Riesi/bierdeckel/code/beercoaster/build.rs

use vergen_gitcl::{
    BuildBuilder, CargoBuilder, Emitter, GitclBuilder, RustcBuilder, SysinfoBuilder,
};

fn main() -> Result<(), Box<dyn std::error::Error>> {
    embuild::espidf::sysenv::output();
    // NOTE: This will output only the instructions specified.
    // NOTE: See the specific builder documentation for configuration options. 
    let build = BuildBuilder::all_build()?;
    let cargo = CargoBuilder::all_cargo()?;
    let gitcl = GitclBuilder::default().describe(true, true, None).dirty(true).build()?;
    let rustc = RustcBuilder::all_rustc()?;
    let si = SysinfoBuilder::all_sysinfo()?;

    Emitter::default()
        .add_instructions(&build)?
        .add_instructions(&cargo)?
        .add_instructions(&gitcl)?
        .add_instructions(&rustc)?
        .add_instructions(&si)?
        .emit()?;
    Ok(())
}
