Riesi/bierdeckel/code/flasher_gui/src/main.rs

use iced::widget::{button, center, column, combo_box, pick_list, scrollable, text_editor, space, text, progress_bar};
use iced::{Center, Element, Fill, Task, Theme};
use rfd::{AsyncFileDialog, FileHandle};

use btleplug::platform::Manager;
use btleplug::platform::Adapter;
pub mod bt_util;
use crate::bt_util::{OTAControlResponse, OTAControl};
use std::time::{Duration, SystemTime, UNIX_EPOCH};
use tokio::time;

/*
#[tokio::main]
async fn main() -> Result<(), Box<dyn Error>> {
    let manager = Manager::new().await?;
    let adapter_list = manager.adapters().await?;
    if adapter_list.is_empty() {
        eprintln!("No Bluetooth adapters found");
    }
    // Flash
    scan(&adapter_list, false).await.unwrap();

    // Delay to prevent 
    time::sleep(Duration::from_millis(4000)).await;

    // Verify
    scan(&adapter_list, true).await.unwrap();

    Ok(())
}*/

pub fn main() -> iced::Result {
    if let Some(timestamp) = option_env!("VERGEN_BUILD_TIMESTAMP") {
        println!("Build Timestamp: {timestamp}");
    }
    if let Some(describe) = option_env!("VERGEN_GIT_DESCRIBE") {
        println!("git describe: {describe}");
    }
    
    iced::run(Example::update, Example::view)
}

struct Example {
    languages: [Language;2],
    selected_language: Option<Language>,
    text: String,
    flash_file_path: Option<FileHandle>,
    bt_adapter_list: Option<Vec<Adapter>>,
    progress: f32,
    content: text_editor::Content,
}

#[derive(Debug, Clone)]
enum Message {
    Selected(Language),
    OptionHovered(Language),
    Button(Origin),
    File(Option<FileHandle>),
    Bluetooth(BTOrigin),
    Closed,
}
#[derive(Debug, Clone)]
enum Origin {
    FlashBin,
    Flash,
    Search,
}

#[derive(Debug, Clone)]
enum BTOrigin {
    SearchResult(Option<Vec<Adapter>>),
}

async fn flashy(bin_file: FileHandle) -> Option<Vec<Adapter>> {
    if let Ok(manager) = Manager::new().await {
    
        if let Ok(adapter_list) = btleplug::api::Manager::adapters(&manager).await {
            if !adapter_list.is_empty() {
                if let Err(_) = bt_util::scan(&adapter_list, false, &bin_file).await {
                    return None;
                }
                time::sleep(Duration::from_millis(4000)).await;

                // Verify
                if let Err(_) = bt_util::scan(&adapter_list, true, &bin_file).await {
                    return None;
                }
                return Some(adapter_list)
                
            }
            eprintln!("No Bluetooth adapters found");
        }
    }
    None
}

impl Example {
    fn new() -> Self {
        Self {
            languages: Language::ALL,
            selected_language: None,
            text: String::new(),
            flash_file_path: None,
            bt_adapter_list: None,
            progress: 25f32,
            content: text_editor::Content::new(),
        }
    }

    fn update(&mut self, message: Message) -> Task<Message>  {
        match message {
            Message::Button(ori) => {
                match ori {
                    Origin::Flash => {
                        Task::none()
                    }
                    Origin::FlashBin => {
                        let file_picker = AsyncFileDialog::new()
                                    .add_filter("bin", &["bin"])
                                    .set_directory(".")
                                    .pick_file();
                        Task::perform( file_picker, Message::File)
                    }
                    Origin::Search => {
                        if let None = self.bt_adapter_list {
                            if let Some(file) = &self.flash_file_path {
                                return Task::perform( flashy(file.clone()), |av| Message::Bluetooth(BTOrigin::SearchResult(av)))
                            }
                        }
                        Task::none()
                    }
                }
            }
            Message::Bluetooth(bt) => {
                match bt {    
                    BTOrigin::SearchResult(av) => {
                        if let Some(av) = av {
                            
                        }
                        Task::none()
                    }
                }
            }
            Message::File(file) => {
                if let Some(file) = file {
                    let file_path= &file.path().display();
                    println!("{}",file_path);
                    self.text = file_path.to_string();
                    self.flash_file_path = Some(file);
                }
                Task::none()
            }
            Message::Selected(language) => {
                self.selected_language = Some(language);
                self.text = language.hello().to_string();
                Task::none()
            }
            Message::OptionHovered(language) => {
                self.text = language.hello().to_string();
                Task::none()
            }
            Message::Closed => {
                self.text = self
                    .selected_language
                    .map(|language| language.hello().to_string())
                    .unwrap_or_default();
                Task::none()
            }
        }
    }

    fn view(&self) -> Element<'_, Message> {
        // Buttons
        let button_bin_picker = button("pick binary file...").on_press(Message::Button(Origin::FlashBin));
        let button_search = button("search for coasters...").on_press(Message::Button(Origin::Search));
        let button_connect = button("connect to coaster...").on_press(Message::Button(Origin::Flash));
        let button_flash = button("flash").on_press(Message::Button(Origin::Flash));

        let prog_bar = progress_bar::<Theme>(0.0..=100.0, self.progress);
        let console_log = text_editor(&self.content)
        .placeholder("Type something here...\n multi \n ine\n\nhlello").min_height(300).height(800).width(1000); //.on_action(Message::Edit);

        let scro = scrollable(column![
            console_log,
        ]).height(300);
        // let combo_box = combo_box(
        //     &self.languages,
        //     "Type a language...",
        //     self.selected_language.as_ref(),
        //     Message::Selected,
        // )
        // .on_option_hovered(Message::OptionHovered)
        // .on_close(Message::Closed)
        // .width(250);

        let combo_box = pick_list(
            self.languages,
            self.selected_language,
            Message::Selected,
        ).on_close(Message::Closed)
        .width(250);

        // Layout
        let content = column![
            button_bin_picker,
            button_search,
            button_connect,
            button_flash,
            text(&self.text),
            "What is your language?",
            combo_box,
            prog_bar,
            "Console:",
            scro,
            space().height(150),
        ]
        .width(Fill)
        .align_x(Center)
        .spacing(10);

        center(scrollable(content)).into()
    }
}

impl Default for Example {
    fn default() -> Self {
        Example::new()
    }
}

#[derive(Debug, Clone, Copy, PartialEq, Eq, Default)]
pub enum Language {
    #[default]
    Danish,
    Other,
}

impl Language {
    const ALL: [Language; 2] = [
        Language::Danish,
        Language::Other,
    ];

    fn hello(&self) -> &str {
        match self {
            Language::Danish => "Halloy!",
            Language::Other => "... hello?",
        }
    }
}

impl std::fmt::Display for Language {
    fn fmt(&self, f: &mut std::fmt::Formatter<'_>) -> std::fmt::Result {
        write!(
            f,
            "{}",
            match self {
                Language::Danish => "Danish",
                Language::Other => "Some other language",
            }
        )
    }
}
